telzo2000/cool337/img/img00003.jpg

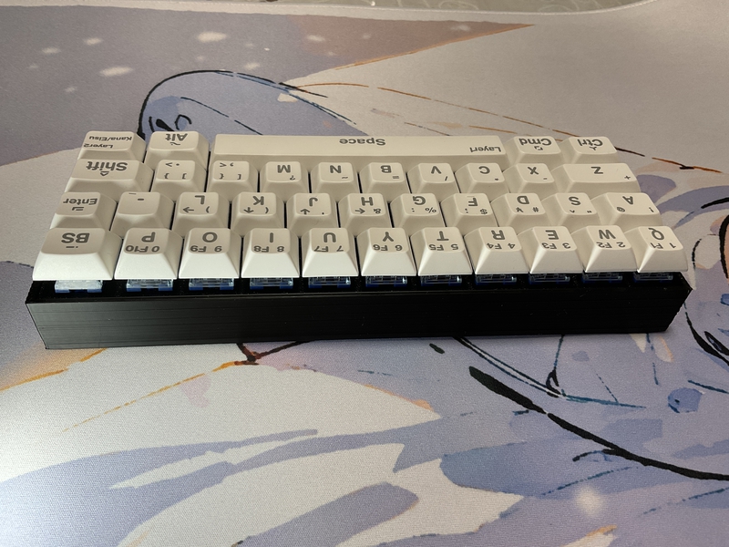
img/img00003.jpg
