telzo2000/cool337/img/img00004.jpg

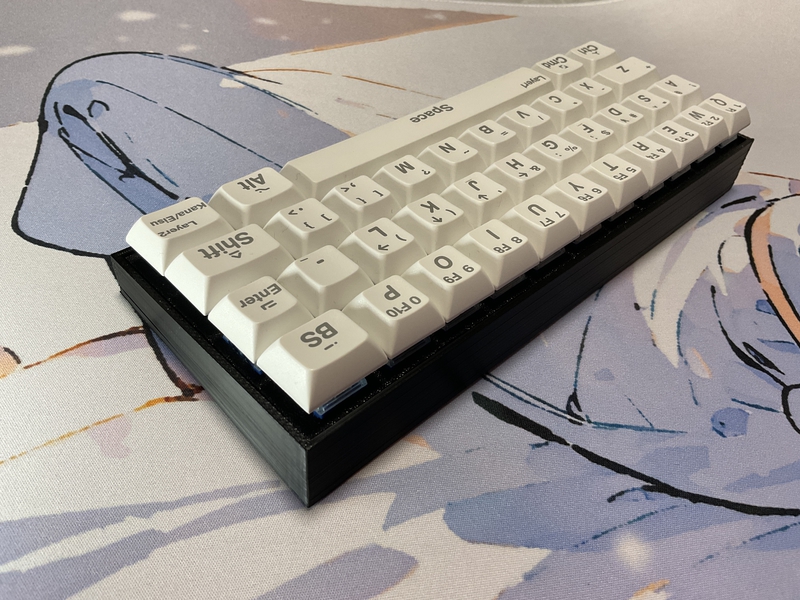
img/img00004.jpg
