telzo2000/cool337/img/img00008.jpg

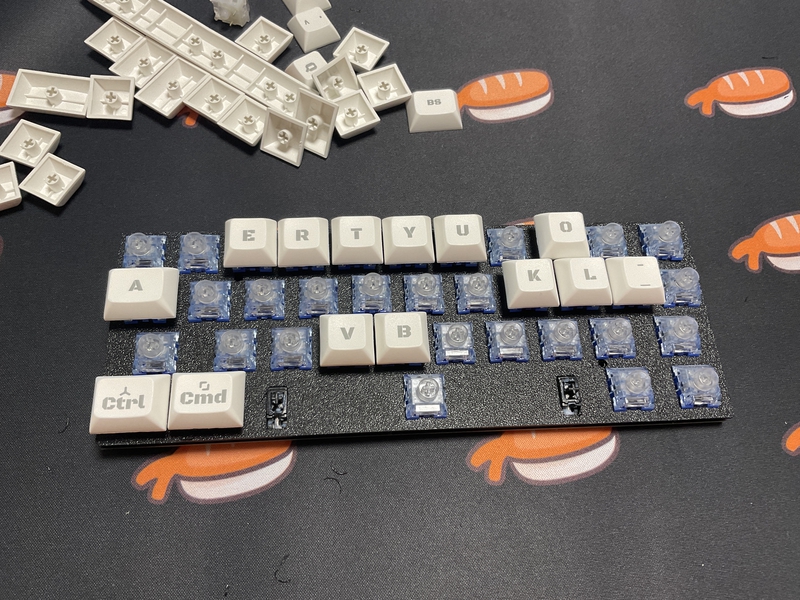
img/img00008.jpg
