telzo2000/cool337/img/img00010.jpg

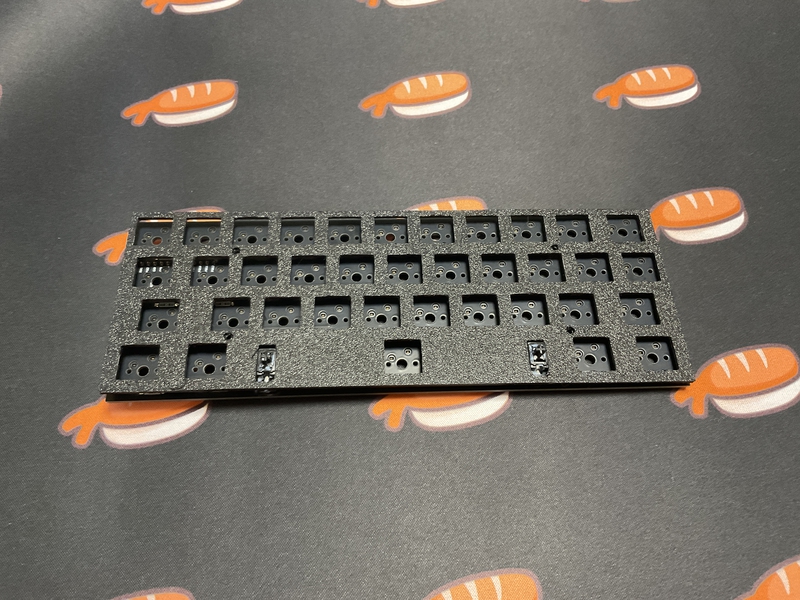
img/img00010.jpg
