telzo2000/cool337/img/img00012.jpg

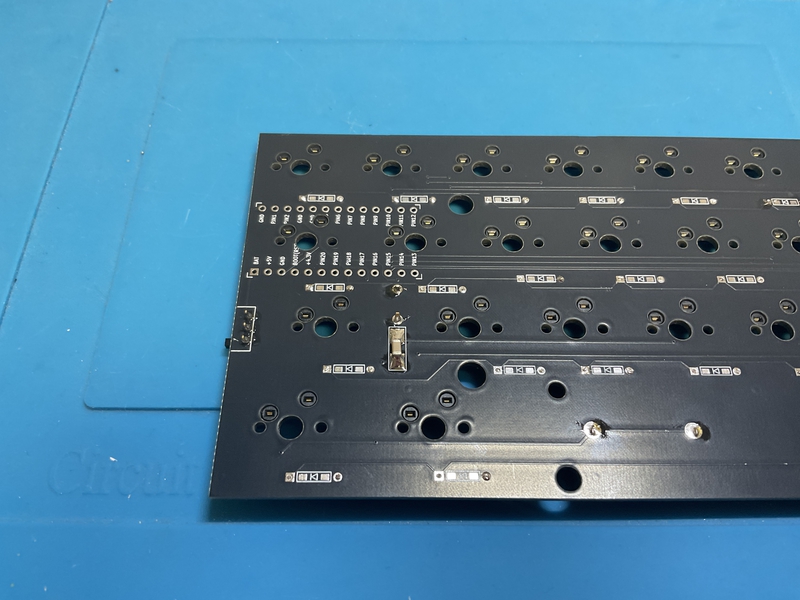
img/img00012.jpg
